ok1fet/LoRa-WX-station/pictures/LoRaWX01.jpg

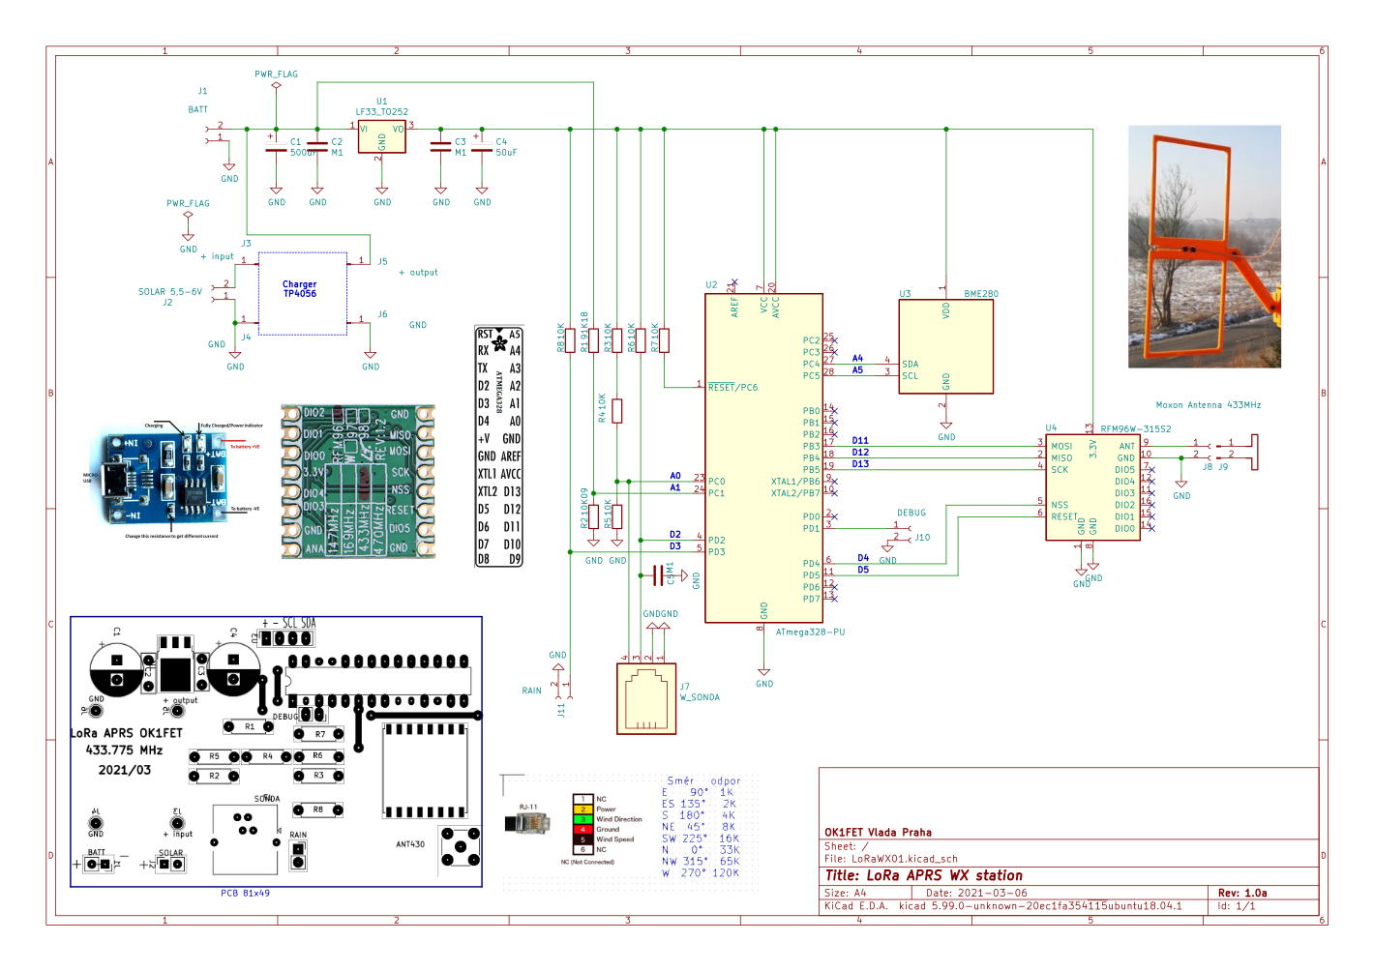
pictures/LoRaWX01.jpg
